Jed0vcela/VFD_V1/Kicad_files/VFD 90deg.STEP

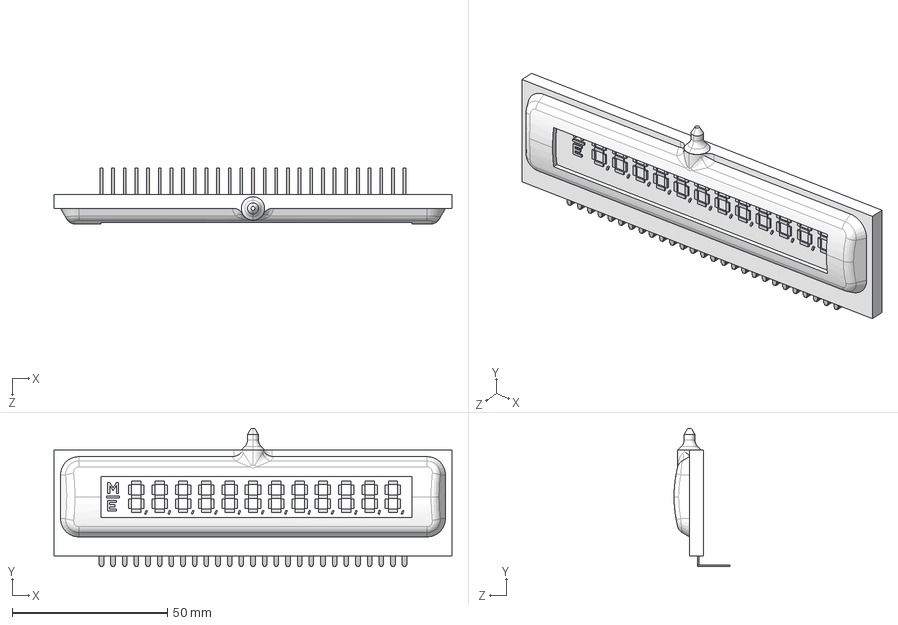
[picture p1: CAD file, 2025-11-04]
Kicad_files/VFD 90deg.STEP
128.0 x 44.5 x 18.0 mm
