Jed0vcela/VFD_V1/Kicad_files/VFD v1.STEP

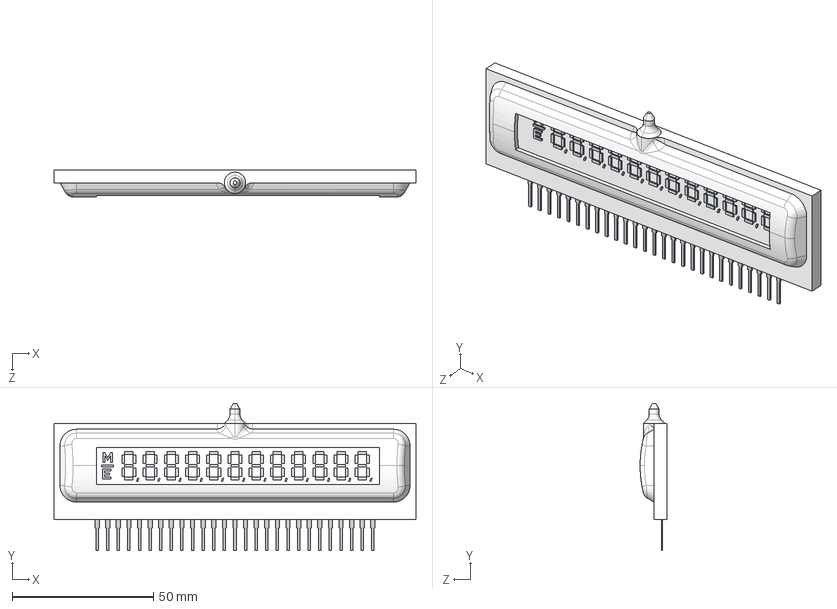
[picture p2: CAD file, 2025-11-04]
Kicad_files/VFD v1.STEP
128.0 x 52.0 x 9.50 mm
