Jed0vcela/VFD_V1/Kicad_files/3D files/Part1^VFD display 1.STL

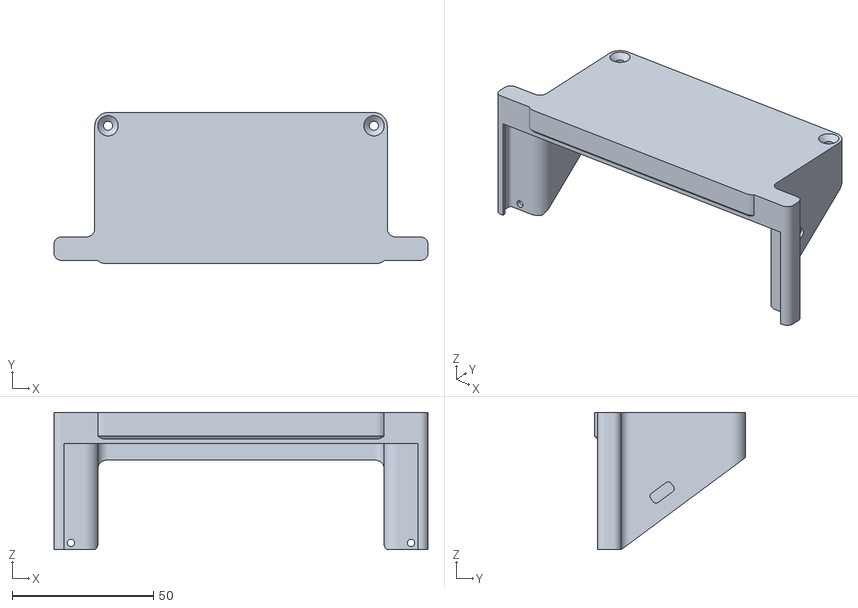
[picture p3: CAD file, 2026-01-22]
Kicad_files/3D files/Part1^VFD display 1.STL
132.2 x 53.4 x 48.6
